Pejo-306/digital-function-generator-v2/software/DFGv2-Firmware.X/include/DFG-firmware/IOexpander_driver.h

/* 
 * File:   IOexpander_driver.h
 * Author: pesho
 *
 * Created on February 24, 2020, 12:34 PM
 */

#ifndef IOEXPANDER_DRIVER_H
#define	IOEXPANDER_DRIVER_H

#include <inttypes.h>

#include "defs.h"

#define IOEX_RESET_TIME 10  // in us

#ifdef	__cplusplus
extern "C" {
#endif

void ioex_reset(void);

uint8_t ioex_set_iodir(uint8_t address, uint8_t dir, fbool options);

uint8_t ioex_set_gppu(uint8_t address, uint8_t gppu, fbool options);

uint8_t ioex_write_gpio(uint8_t address, uint8_t data, fbool options);

uint8_t ioex_read_gpio(uint8_t address, uint8_t *data, fbool options);

uint8_t ioex_read_olat(uint8_t address, uint8_t *data, fbool options);

#ifdef	__cplusplus
}
#endif

#endif	/* IOEXPANDER_DRIVER_H */
