Pejo-306/digital-function-generator-v2/software/DFGv2-Firmware.X/include/DFG-firmware/waveforms.h

/* 
 * File:   waveforms.h
 * Author: pesho
 *
 * Created on May 9, 2020, 3:50 PM
 */

#ifndef WAVEFORMS_H
#define	WAVEFORMS_H

#include <inttypes.h>
#include <avr/pgmspace.h>

#define SINE_SIZE   4096
#define TRI_SIZE    4096
#define SQ_SIZE     1024

#ifdef	__cplusplus
extern "C" {
#endif

static const uint16_t sine_wave[SINE_SIZE] PROGMEM = {
    0x8000, 0x8030, 0x8060, 0x8090, 0x80c0, 0x80f0, 0x8120, 0x8150, 
    0x8190, 0x81c0, 0x81f0, 0x8220, 0x8250, 0x8280, 0x82b0, 0x82f0, 
    0x8320, 0x8350, 0x8380, 0x83b0, 0x83e0, 0x8410, 0x8450, 0x8480, 
    0x84b0, 0x84e0, 0x8510, 0x8540, 0x8570, 0x85b0, 0x85e0, 0x8610, 
    0x8640, 0x8670, 0x86a0, 0x86d0, 0x8710, 0x8740, 0x8770, 0x87a0, 
    0x87d0, 0x8800, 0x8830, 0x8860, 0x88a0, 0x88d0, 0x8900, 0x8930, 
    0x8960, 0x8990, 0x89c0, 0x8a00, 0x8a30, 0x8a60, 0x8a90, 0x8ac0, 
    0x8af0, 0x8b20, 0x8b50, 0x8b90, 0x8bc0, 0x8bf0, 0x8c20, 0x8c50, 
    0x8c80, 0x8cb0, 0x8ce0, 0x8d20, 0x8d50, 0x8d80, 0x8db0, 0x8de0, 
    0x8e10, 0x8e40, 0x8e70, 0x8eb0, 0x8ee0, 0x8f10, 0x8f40, 0x8f70, 
    0x8fa0, 0x8fd0, 0x9000, 0x9030, 0x9070, 0x90a0, 0x90d0, 0x9100, 
    0x9130, 0x9160, 0x9190, 0x91c0, 0x91f0, 0x9230, 0x9260, 0x9290, 
    0x92c0, 0x92f0, 0x9320, 0x9350, 0x9380, 0x93b0, 0x93f0, 0x9420, 
    0x9450, 0x9480, 0x94b0, 0x94e0, 0x9510, 0x9540, 0x9570, 0x95a0, 
    0x95e0, 0x9610, 0x9640, 0x9670, 0x96a0, 0x96d0, 0x9700, 0x9730, 
    0x9760, 0x9790, 0x97c0, 0x9800, 0x9830, 0x9860, 0x9890, 0x98c0, 
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
    0x8000, 0x8000, 0x8000, 0x8000, 0x8000, 0x8000, 0x8000, 0x8000,
    0x8000, 0x8000, 0x8000, 0x8000, 0x8000, 0x8000, 0x8000, 0x8000,
    0x8000, 0x8000, 0x8000, 0x8000, 0x8000, 0x8000, 0x8000, 0x8000,
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
};
    
#ifdef	__cplusplus
}
#endif

#endif	/* WAVEFORMS_H */
